JakobThiessen/NixieClock/software/NixieClock/src/png/Advent_1.jpg

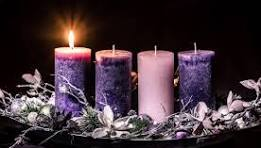
software/NixieClock/src/png/Advent_1.jpg
