JakobThiessen/NixieClock/software/NixieClock/src/png/Advent_2.jpg

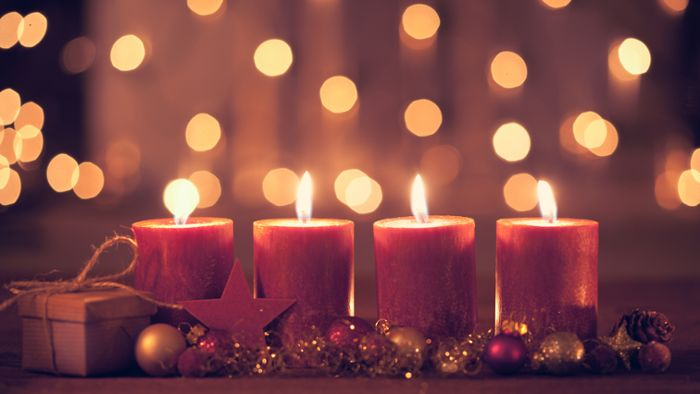
software/NixieClock/src/png/Advent_2.jpg
