JakobThiessen/NixieClock/software/NixieClock/src/png/advent_kerze.jpg

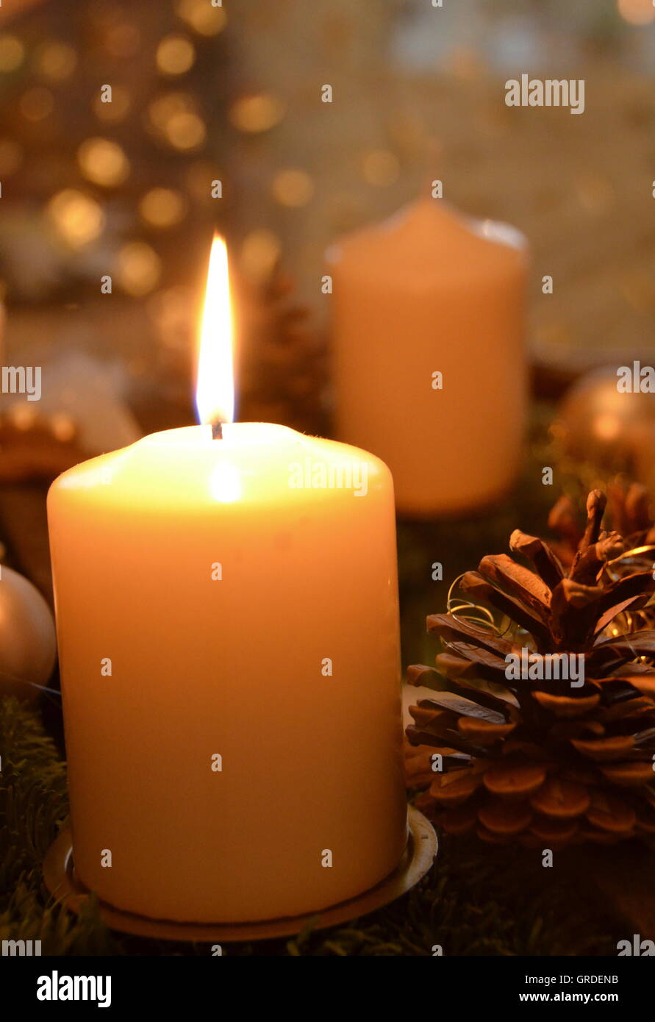
software/NixieClock/src/png/advent_kerze.jpg
