JakobThiessen/NixieClock/software/NixieClock/src/SD_CARD/pict/birthday_19th_2.jpeg

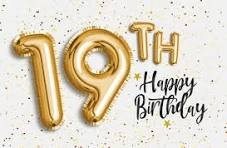
software/NixieClock/src/SD_CARD/pict/birthday_19th_2.jpeg
