JakobThiessen/NixieClock/software/NixieClock/src/background_1.h

#include <stdint.h>

const uint16_t background_1[] PROGMEM = {
0x2230, 0x2a92, 0x2a72, 0x2a72, 0x2a72, 0x2a72, 0x2a72, 0x2a72, 0x2a72, 0x2a72, 0x2a72, 0x2a72, 0x2a72, 0x2a72, 0x2a72, 0x2272, 0x2272, 0x2272, 0x2272, 0x2272, 0x2272, 0x2271, 0x2271, 0x2271, 0x2271, 0x2271, 0x2271, 0x2271, 0x2271, 0x2271, 0x2251, 0x2251, 0x2251, 0x2251, 0x2251, 0x2251, 0x2251, 0x2251, 0x2251, 0x2251, 0x2251, 0x2251, 0x2251, 0x2251, 0x2251, 0x2251, 0x2251, 0x2251, 0x2251, 0x2251, 0x2251, 0x2250, 0x2251, 0x2250, 0x2250, 0x2250, 0x2230, 0x2230, 0x2230, 0x2230, 0x2230, 0x2230, 0x2230, 0x2230, 0x2230, 0x2230, 0x2230, 0x2230, 0x2230, 0x2230, 0x2230, 0x2230, 0x2230, 0x2230, 0x2230, 0x2230, 0x2230, 0x2230, 0x2230, 0x2230, 0x2230, 0x2230, 0x2230, 0x220f, 0x220f, 0x220f, 0x220f, 0x220f, 0x220f, 0x220f, 0x220f, 0x220f, 0x220f, 0x220f, 0x220f, 0x220f, 0x220f, 0x220f, 0x220f, 0x220f, 0x220f, 0x220f, 0x220f, 0x220f, 0x220f, 0x220f, 0x220f, 0x220f, 0x220f, 0x1a0f, 0x19ef, 0x19ef, 0x19ef, 0x19ef, 0x19ee, 0x19ee, 0x19ee, 0x19ee, 0x19ee, 0x19ee, 0x19ee, 0x19ee, 0x19ee, 0x19ee, 0x19ee, 0x19ee, 0x19ee, 0x19ee, 0x19ee, 0x19ee, 0x19ee, 0x19ee, 0x19ee, 0x19ee, 0x19ee, 0x19ee, 0x19ee, 0x19ce, 0x19ee, 0x19ee, 0x19ee, 0x19ce, 0x19ce, 0x19ce, 0x19ce, 0x19ce, 0x19ce, 0x19cd, 0x19cd, 0x19cd, 0x19cd, 0x19cd, 0x19cd, 0x19cd, 0x19cd, 0x19cd, 0x19cd, 0x19cd, 0x19cd, 0x19ac, 
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
};
