JakobThiessen/NixieClock/software/NixieClock/src/img_advent.h

#ifndef IMG_ADVENT_h
#define IMG_ADVENT_h

#include <stdint.h>

const uint16_t bg_advent_1[] PROGMEM = {

};

//128x227
const uint16_t bg_advent_2[] PROGMEM = {
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
};

#endif /* IMG_ADVENT_h */
